florian-ariasu/ebook-reader/Images/3d-model-3.png

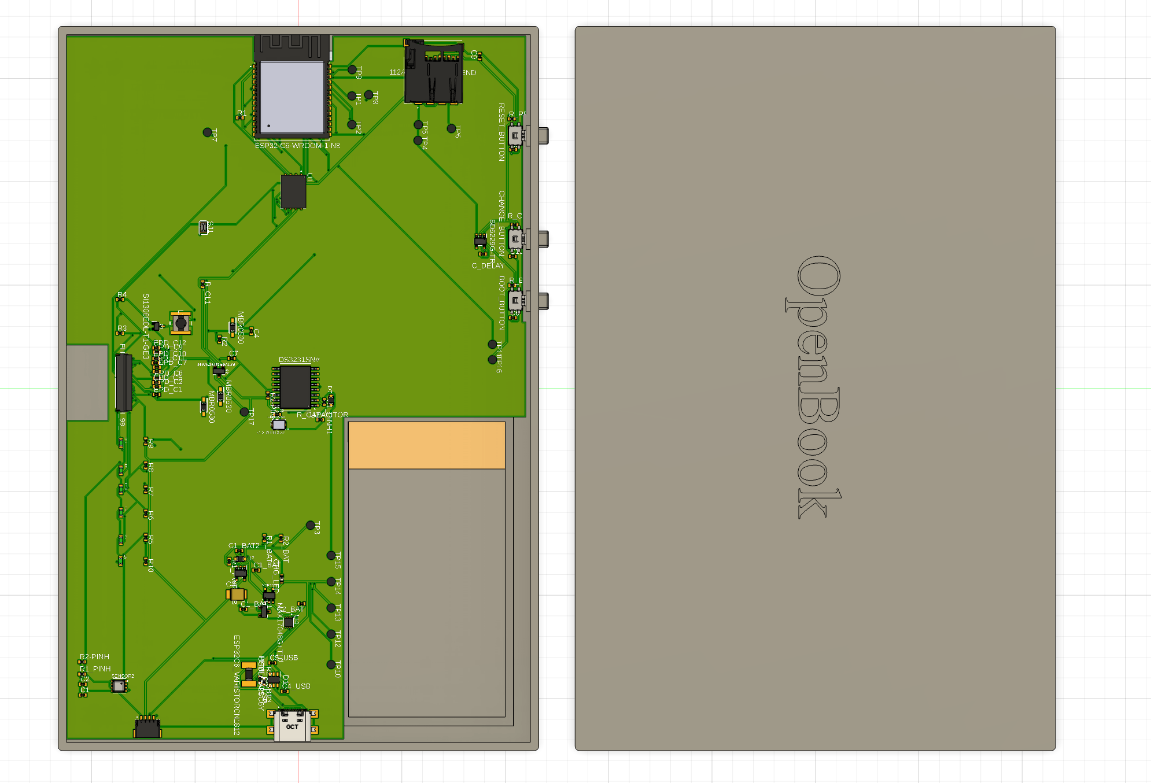
Images/3d-model-3.png
